KrHaaland/GNSS_Alarm_Clock/src/Settings.cpp

// Settings.cpp — persistent settings packed into the RV-3028's 43-byte user
// EEPROM. Chosen over the old internal-flash emulation because the RTC EEPROM
// survives firmware reflashes (the flash area lived inside the app image and
// was wiped on every update), takes ~100k writes/byte (4x internal flash),
// and lets the 24LC512 be dropped from the hardware-v2 BOM.
//
// The RAM struct keeps its friendly layout; pack()/unpack() translate to a
// 39-byte image. Space is won by not storing derived data:
//   - tz strings (68 B) -> lat/lon in centidegrees + manual-zone index; the
//     POSIX string is re-derived at boot via tz_lookup()/TZ_TABLE.
//   - alarm tune filename (32 B) -> 16-bit FNV-1a hash, re-matched against
//     the TUNES directory at boot (missing file -> builtin melody fallback).
// Writes go byte-by-byte (~16 ms each) and only for bytes that changed; the
// checksum byte is written LAST so a torn write invalidates the block
// (-> defaults on next boot) instead of going unnoticed.
#include "Settings.h"

#include <string.h>

#include "RtcRV3028.h"
#include "Timezone.h"
#include "TuneStorage.h"
#include "TzTable.h"

// --- packed image layout -----------------------------------------------------
#define PACK_MAGIC0 'G'
#define PACK_MAGIC1 'C'
#define PACK_VERSION 4 // v4: snoozeTotal u32 -> u24, spare byte dropped
#define PACK_LEN 38           // incl. trailing checksum; <= RTC_USER_EEPROM_SIZE
#define EPOCH2020_DAYS 18262u // 2020-01-01 in unix epoch-days (weekStart base)

enum : uint8_t {
  OFF_MAGIC0 = 0, OFF_MAGIC1, OFF_VERSION, OFF_FLAGS,
  OFF_LAT = 4,    // i16 centideg, LE
  OFF_LON = 6,    // i16 centideg
  OFF_ZONEIDX = 8, // manual TZ_TABLE index, 0xFF = none
  OFF_VOLUME, OFF_SNOOZEMIN, OFF_BUZZAFTER, OFF_BRIGHT,
  OFF_DIMTIMEOUT = 13, // u16 seconds
  OFF_DIMBRIGHT = 15,
  OFF_SNZTOTAL = 16,   // u24 LE (caps at 16.7M snoozes)
  OFF_SNZWEEK = 19,    // u16
  OFF_SNZWEEKSTART = 21, // u16, local epoch-day - EPOCH2020_DAYS
  OFF_ALARM0 = 23,     // 7 B each: flags,hour,min,mask,melody,hash(u16)
  OFF_ALARM1 = 30,
  OFF_CHECKSUM = 37,
};
// v3 image (40 B): snoozeTotal was u32 so everything from SNZWEEK on sat one
// byte later, plus a spare byte before the checksum. LE means the u24 keeps
// the same three bytes — migration drops the (always 0) MSB and shifts.
enum : uint8_t {
  V3_SNZWEEK = 20, V3_ALARM0 = 24, V3_ALARM1 = 31,
  V3_RESERVED = 38, V3_CHECKSUM = 39, V3_LEN = 40,
};
#define V1_LEN 39 // v1 image: 38-byte payload, checksum at offset 38
// alarm flags byte: b0 enabled, b1-2 gentle-wake ramp index (see kRampSecs),
// b3-4 random-jitter index (see kJitterMin; older v3 images have 00 = off,
// which reads back compatibly - no version bump needed), b5 lights-OFF
// (inverted so old blocks' 0 = LED show on, again no version bump)
static const uint8_t kRampSecs[4] = {0, 15, 30, 60};
static const uint8_t kJitterMin[4] = {0, 1, 5, 9};
static uint8_t jitter_idx(uint8_t m) {
  for (uint8_t i = 3; i > 0; i--)
    if (m >= kJitterMin[i])
      return i;
  return 0;
}
static uint8_t ramp_idx(uint8_t secs) {
  for (uint8_t i = 3; i > 0; i--)
    if (secs >= kRampSecs[i])
      return i;
  return 0;
}
// flags byte: b0 tzAuto, b1 tapSnooze, b2 use24h, b3 havePosition, b4-5 mode,
// b6 starryNight (added post-v3; old blocks carry 0 = off, no version bump)
// alarm flags byte: b0 enabled

static Settings s;
static uint8_t lastPacked[PACK_LEN];
static bool haveLast = false;

// 16-bit FNV-1a of a filename (folded 32-bit); 0 is reserved for "no tune".
static uint16_t tune_hash(const char *name) {
  if (!name || !name[0])
    return 0;
  uint32_t h = 2166136261u;
  for (const char *p = name; *p; p++) {
    h ^= (uint8_t)*p;
    h *= 16777619u;
  }
  uint16_t f = (uint16_t)((h >> 16) ^ h);
  return f ? f : 1;
}

static void put16(uint8_t *b, uint16_t v) { b[0] = v & 0xFF; b[1] = v >> 8; }
static void put24(uint8_t *b, uint32_t v) {
  if (v > 0xFFFFFFul)
    v = 0xFFFFFFul;
  b[0] = v & 0xFF; b[1] = (v >> 8) & 0xFF; b[2] = (v >> 16) & 0xFF;
}
static uint16_t get16(const uint8_t *b) {
  return (uint16_t)(b[0] | (b[1] << 8));
}
static uint32_t get24(const uint8_t *b) {
  return (uint32_t)b[0] | ((uint32_t)b[1] << 8) | ((uint32_t)b[2] << 16);
}

static int16_t centideg(float v) {
  float c = v * 100.0f;
  if (c > 32767.0f) c = 32767.0f;
  if (c < -32768.0f) c = -32768.0f;
  return (int16_t)(c >= 0 ? c + 0.5f : c - 0.5f);
}

static uint8_t checksum(const uint8_t *b, uint8_t csOff) {
  uint8_t sum = 0;
  for (uint8_t i = 0; i < csOff; i++)
    sum = (uint8_t)(sum + b[i]);
  return (uint8_t)(0xFF - sum); // so full-block sum == 0xFF when intact
}

static void pack(const Settings &in, uint8_t out[PACK_LEN]) {
  memset(out, 0, PACK_LEN);
  out[OFF_MAGIC0] = PACK_MAGIC0;
  out[OFF_MAGIC1] = PACK_MAGIC1;
  out[OFF_VERSION] = PACK_VERSION;
  out[OFF_FLAGS] = (in.tzAuto ? 1 : 0) | (in.tapSnooze ? 2 : 0) |
                   (in.use24h ? 4 : 0) | (in.havePosition ? 8 : 0) |
                   ((in.mode & 3) << 4) | (in.starryNight ? 0x40 : 0);
  put16(&out[OFF_LAT], (uint16_t)centideg(in.lastLat));
  put16(&out[OFF_LON], (uint16_t)centideg(in.lastLon));
  int zi = tztable_index_of_posix(in.tzPosix);
  out[OFF_ZONEIDX] = (zi >= 0 && zi < 0xFF) ? (uint8_t)zi : 0xFF;
  out[OFF_VOLUME] = in.volume;
  out[OFF_SNOOZEMIN] = in.snoozeMinutes;
  out[OFF_BUZZAFTER] = in.buzzerAfterMin;
  out[OFF_BRIGHT] = in.brightness;
  put16(&out[OFF_DIMTIMEOUT], in.dimTimeoutS);
  out[OFF_DIMBRIGHT] = in.dimBrightness;
  put24(&out[OFF_SNZTOTAL], in.snoozeTotal);
  put16(&out[OFF_SNZWEEK], in.snoozeWeek);
  uint32_t ws = in.snoozeWeekStart;
  ws = (ws > EPOCH2020_DAYS) ? ws - EPOCH2020_DAYS : 0;
  put16(&out[OFF_SNZWEEKSTART], (uint16_t)(ws > 0xFFFF ? 0xFFFF : ws));
  for (uint8_t i = 0; i < NUM_ALARMS; i++) {
    uint8_t *a = &out[i == 0 ? OFF_ALARM0 : OFF_ALARM1];
    const AlarmConfig &ac = in.alarms[i];
    a[0] = (uint8_t)((ac.enabled ? 1 : 0) | (ramp_idx(ac.rampSeconds) << 1) |
                     (jitter_idx(ac.jitterMinutes) << 3) |
                     (ac.lights ? 0 : 0x20));
    a[1] = ac.hour;
    a[2] = ac.minute;
    a[3] = ac.daysMask;
    a[4] = ac.melodyId;
    put16(&a[5], tune_hash(ac.tune));
  }
  out[OFF_CHECKSUM] = checksum(out, OFF_CHECKSUM);
}

// Tune hashes seen at unpack; resolved against the TUNES directory once
// storage is up (settings_begin runs after storage_begin — see main.cpp).
static uint16_t s_pendingTuneHash[NUM_ALARMS];

static void resolve_tunes() {
  char names[12][32];
  uint8_t n = storage_list_tunes(names, 12);
  for (uint8_t i = 0; i < NUM_ALARMS; i++) {
    s.alarms[i].tune[0] = '\0';
    uint16_t want = s_pendingTuneHash[i];
    if (!want)
      continue;
    for (uint8_t k = 0; k < n; k++)
      if (tune_hash(names[k]) == want) {
        strncpy(s.alarms[i].tune, names[k], TUNE_NAME_LEN - 1);
        s.alarms[i].tune[TUNE_NAME_LEN - 1] = '\0';
        break;
      }
    // no match -> stays "", alarm falls back to the builtin melody
  }
}

static void unpack(const uint8_t in[PACK_LEN], Settings &out) {
  settings_defaults(); // sane base; overwrite with stored values
  uint8_t f = in[OFF_FLAGS];
  out.tzAuto = f & 1;
  out.tapSnooze = f & 2;
  out.use24h = f & 4;
  out.havePosition = f & 8;
  out.mode = (uint8_t)((f >> 4) & 3) % MODE_COUNT;
  out.starryNight = f & 0x40;
  out.lastLat = (int16_t)get16(&in[OFF_LAT]) / 100.0f;
  out.lastLon = (int16_t)get16(&in[OFF_LON]) / 100.0f;
  out.volume = in[OFF_VOLUME] <= 10 ? in[OFF_VOLUME] : 10;
  out.snoozeMinutes = in[OFF_SNOOZEMIN] ? in[OFF_SNOOZEMIN] : 9;
  out.buzzerAfterMin = in[OFF_BUZZAFTER];
  out.brightness = in[OFF_BRIGHT];
  out.dimTimeoutS = get16(&in[OFF_DIMTIMEOUT]);
  out.dimBrightness = in[OFF_DIMBRIGHT];
  out.snoozeTotal = get24(&in[OFF_SNZTOTAL]);
  out.snoozeWeek = get16(&in[OFF_SNZWEEK]);
  out.snoozeWeekStart = EPOCH2020_DAYS + get16(&in[OFF_SNZWEEKSTART]);
  for (uint8_t i = 0; i < NUM_ALARMS; i++) {
    const uint8_t *a = &in[i == 0 ? OFF_ALARM0 : OFF_ALARM1];
    AlarmConfig &ac = out.alarms[i];
    ac.enabled = a[0] & 1;
    ac.rampSeconds = kRampSecs[(a[0] >> 1) & 3];
    ac.jitterMinutes = kJitterMin[(a[0] >> 3) & 3];
    ac.lights = !(a[0] & 0x20);
    ac.hour = a[1] <= 23 ? a[1] : 7;
    ac.minute = a[2] <= 59 ? a[2] : 0;
    ac.daysMask = a[3] & 0x7F;
    ac.melodyId = a[4];
    ac.tune[0] = '\0';
    s_pendingTuneHash[i] = get16(&a[5]);
  }
  // Re-derive the timezone strings the pack dropped: manual selection from
  // the GMT ladder, else from the stored position (identical result to what
  // was displayed when it was saved).
  uint8_t zi = in[OFF_ZONEIDX];
  if (!out.tzAuto && zi < TZ_COUNT) {
    strncpy(out.tzPosix, TZ_TABLE[zi].posix, TZ_POSIX_LEN - 1);
    out.tzPosix[TZ_POSIX_LEN - 1] = '\0';
    strncpy(out.tzName, TZ_TABLE[zi].name, TZ_NAME_LEN - 1);
    out.tzName[TZ_NAME_LEN - 1] = '\0';
  } else if (out.havePosition) {
    TzResult r;
    tz_lookup(out.lastLat, out.lastLon, r);
    strncpy(out.tzPosix, r.posix, TZ_POSIX_LEN - 1);
    out.tzPosix[TZ_POSIX_LEN - 1] = '\0';
    strncpy(out.tzName, r.name, TZ_NAME_LEN - 1);
    out.tzName[TZ_NAME_LEN - 1] = '\0';
  } // else: defaults (Europe/Oslo) until the first fix
}

void settings_defaults() {
  memset(&s, 0, sizeof(s)); // zero padding too, keeps memcmp guard meaningful
  s.magic = SETTINGS_MAGIC;
  s.version = SETTINGS_VERSION;

  strncpy(s.tzPosix, "CET-1CEST,M3.5.0,M10.5.0/3", TZ_POSIX_LEN - 1);
  strncpy(s.tzName, "Europe/Oslo", TZ_NAME_LEN - 1);
  s.tzAuto = true;

  s.lastLat = 0.0f;
  s.lastLon = 0.0f;
  s.havePosition = false;

  s.alarms[0].enabled = false;
  s.alarms[0].hour = 7;
  s.alarms[0].minute = 0;
  s.alarms[0].daysMask = 0x3E; // Mon..Fri
  s.alarms[0].tune[0] = '\0';
  s.alarms[0].melodyId = 0;
  s.alarms[0].rampSeconds = 30;
  s.alarms[0].jitterMinutes = 0;
  s.alarms[0].lights = true;

  s.alarms[1].enabled = false;
  s.alarms[1].hour = 9;
  s.alarms[1].minute = 0;
  s.alarms[1].daysMask = 0x41; // Sat+Sun
  s.alarms[1].tune[0] = '\0';
  s.alarms[1].melodyId = 2;
  s.alarms[1].rampSeconds = 30;
  s.alarms[1].jitterMinutes = 0;
  s.alarms[1].lights = true;

  s.volume = 7;
  s.snoozeMinutes = 9;
  s.buzzerAfterMin = 5;
  s.tapSnooze = true;

  s.use24h = true;
  s.starryNight = false;
  s.mode = MODE_CLOCK;
  s.brightness = 0x90;
  s.dimTimeoutS = 30;
  s.dimBrightness = 0x10;

  s.snoozeTotal = 0;
  s.snoozeWeek = 0;
  s.snoozeWeekStart = 0;
}

void settings_begin() {
  settings_defaults();
  memset(s_pendingTuneHash, 0, sizeof(s_pendingTuneHash));

  uint8_t img[V3_LEN]; // big enough for the longer pre-v4 images
  if (!rtc_eeprom_read(0, img, V3_LEN)) {
    // RTC absent/unreachable: run on defaults, RAM-only (no persistence).
    haveLast = false;
    return;
  }
  bool magicOk = img[OFF_MAGIC0] == PACK_MAGIC0 && img[OFF_MAGIC1] == PACK_MAGIC1;
  // Pre-v4 images: fix up in place to the v3 byte layout first (the v1/v2
  // ramp moves), then let the shared v3->v4 shift below bring them current.
  bool oldLayout = false;
  if (magicOk && img[OFF_VERSION] == 3 &&
      img[V3_CHECKSUM] == checksum(img, V3_CHECKSUM)) {
    oldLayout = true;
  } else if (magicOk && img[OFF_VERSION] == 2 &&
             img[V3_CHECKSUM] == checksum(img, V3_CHECKSUM)) {
    // v2 -> v3: the global ramp byte (old offset 38) moves into each alarm's
    // flag bits.
    uint8_t rampBits = (uint8_t)(ramp_idx(img[V3_RESERVED] <= 60
                                              ? img[V3_RESERVED] : 30) << 1);
    img[V3_ALARM0] = (uint8_t)((img[V3_ALARM0] & 1) | rampBits);
    img[V3_ALARM1] = (uint8_t)((img[V3_ALARM1] & 1) | rampBits);
    oldLayout = true;
  } else if (magicOk && img[OFF_VERSION] == 1 &&
             img[V1_LEN - 1] == checksum(img, V1_LEN - 1)) {
    // v1 -> v3: no ramp stored anywhere; default 30 s on both alarms.
    uint8_t rampBits = (uint8_t)(ramp_idx(30) << 1);
    img[V3_ALARM0] = (uint8_t)((img[V3_ALARM0] & 1) | rampBits);
    img[V3_ALARM1] = (uint8_t)((img[V3_ALARM1] & 1) | rampBits);
    oldLayout = true;
  }

  if (oldLayout) {
    // v3 -> v4: snoozeTotal shrinks u32 -> u24. Little-endian means its three
    // low bytes already sit at OFF_SNZTOTAL; drop the (always 0) MSB by
    // shifting everything from SNZWEEK through ALARM1 down one byte. The old
    // spare byte (38) falls off the end. Persisting re-checksums as v4.
    memmove(&img[OFF_SNZWEEK], &img[V3_SNZWEEK],
            V3_ALARM1 + 7 - V3_SNZWEEK); // 20..37 -> 19..36
    unpack(img, s);
    resolve_tunes();
    haveLast = false;
    settings_save();
  } else if (magicOk && img[OFF_VERSION] == PACK_VERSION &&
             img[OFF_CHECKSUM] == checksum(img, OFF_CHECKSUM)) {
    unpack(img, s);
    resolve_tunes();
    memcpy(lastPacked, img, PACK_LEN);
    haveLast = true;
  } else {
    // Blank chip / torn write / unknown format: persist the defaults.
    haveLast = false;
    settings_save();
  }
}

Settings &settings() { return s; }

void settings_save() {
  uint8_t img[PACK_LEN];
  pack(s, img);
  if (haveLast && memcmp(lastPacked, img, PACK_LEN) == 0)
    return; // nothing changed
  bool ok = true;
  if (!haveLast) {
    ok = rtc_eeprom_write(0, img, PACK_LEN);
  } else {
    // Write only changed data bytes (16 ms each), checksum last so an
    // interrupted save is detected at next boot instead of read back wrong.
    for (uint8_t i = 0; i < OFF_CHECKSUM && ok; i++)
      if (img[i] != lastPacked[i])
        ok = rtc_eeprom_write(i, &img[i], 1);
    if (ok && img[OFF_CHECKSUM] != lastPacked[OFF_CHECKSUM])
      ok = rtc_eeprom_write(OFF_CHECKSUM, &img[OFF_CHECKSUM], 1);
  }
  if (ok) {
    memcpy(lastPacked, img, PACK_LEN);
    haveLast = true;
  } else {
    haveLast = false; // force a full rewrite on the next save
  }
}
