KrHaaland/GNSS_Alarm_Clock/src/Gnss.h

// Gnss.h — Quectel L86-M33 GNSS receiver on Serial1 (PA22 TX -> L86 RX,
// PA23 RX <- L86 TX), NMEA at 9600 baud, parsed with TinyGPS++.
// L86 RESET_N (PB31) and FORCE_ON (PB00) are left hi-Z; gnss_hw_reset()
// pulses RESET_N low via direct port access.
#pragma once
#include <Arduino.h>
#include <time.h>

void gnss_begin();  // opens Serial1, configures L86 (RMC+GGA, 1 Hz)
void gnss_task();   // call every loop iteration; feeds parser

// True when the receiver reports a valid date+time (fix not required for
// time on many receivers, but we only trust time once date is valid too).
bool gnss_time_valid();
// UTC epoch of the last decoded time + how many ms ago it was received.
// Returns false if no valid time yet.
bool gnss_get_utc(time_t &utc, uint32_t &ageMs);

bool gnss_has_fix();
bool gnss_get_position(float &lat, float &lon); // last valid fix
bool gnss_get_speed_kmph(float &kmph);   // ground speed (RMC), only when fixed
bool gnss_get_altitude_m(float &meters); // MSL altitude (GGA), only when fixed
uint8_t gnss_num_sats();
uint16_t gnss_hdop_x10(); // HDOP * 10, 0xFFFF when unknown
uint32_t gnss_chars_seen(); // diagnostics: raw NMEA chars processed

// Satellites in view (GSV, requested every 5th fix). TinyGPS++ has no GSV
// support, so Gnss.cpp runs its own line parser alongside it.
struct GnssSatInfo {
  uint8_t prn;      // GPS 1-32, SBAS 33-64, GLONASS 65-96 (L86 numbering)
  uint8_t elevDeg;  // 0-90 above horizon
  uint16_t azimDeg; // 0-359, 0 = north
  uint8_t snrDb;    // C/N0 dB-Hz, 0 = in view but not tracked
  char system;      // 'G' = GPS, 'R' = GLONASS
};
// Copies up to maxN satellites into out, GPS first. Returns the count;
// 0 when no GSV data has arrived for >12 s (antenna dead / sim build).
uint8_t gnss_get_sats(GnssSatInfo *out, uint8_t maxN);

void gnss_hw_reset(); // pulse L86 RESET_N (blocks ~110 ms)

#ifdef GNSS_SIM
// Simulated-GNSS hooks (env:sim / -DGNSS_SIM): the SimConsole feeds position +
// UTC from the USB serial console instead of the L86, so the timezone/clock
// pipeline can be exercised on-device without a real fix.
void gnss_sim_set_fix(float lat, float lon); // set position + report a fix
void gnss_sim_clear_fix();                    // drop the simulated fix
void gnss_sim_set_utc(time_t utc);            // seed the UTC clock
void gnss_sim_set_motion(float kmph, float altM); // feed speed/altitude
#endif
